copperheadhq/copperhead-quiet-orbit/images/02-bottom.png

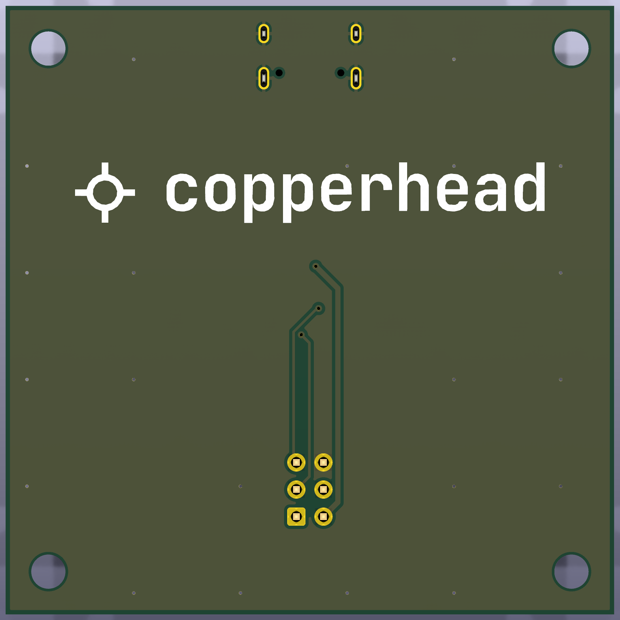
images/02-bottom.png
