copperheadhq/copperhead-quiet-orbit/images/03-iso-front-left.png

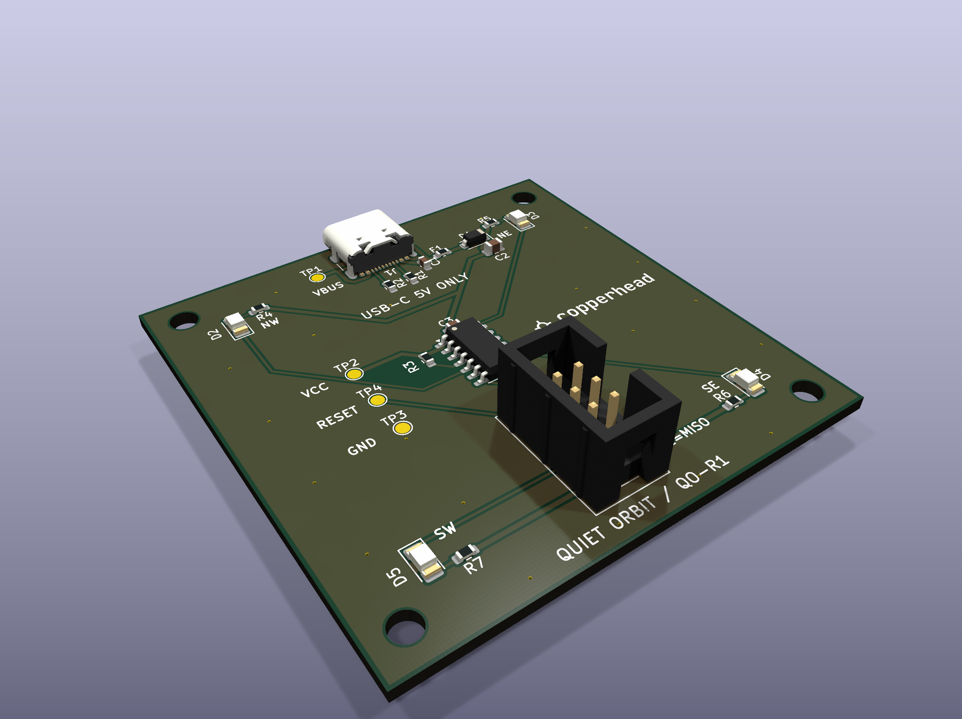
images/03-iso-front-left.png
