copperheadhq/copperhead-quiet-orbit/images/05-iso-rear-usb.png

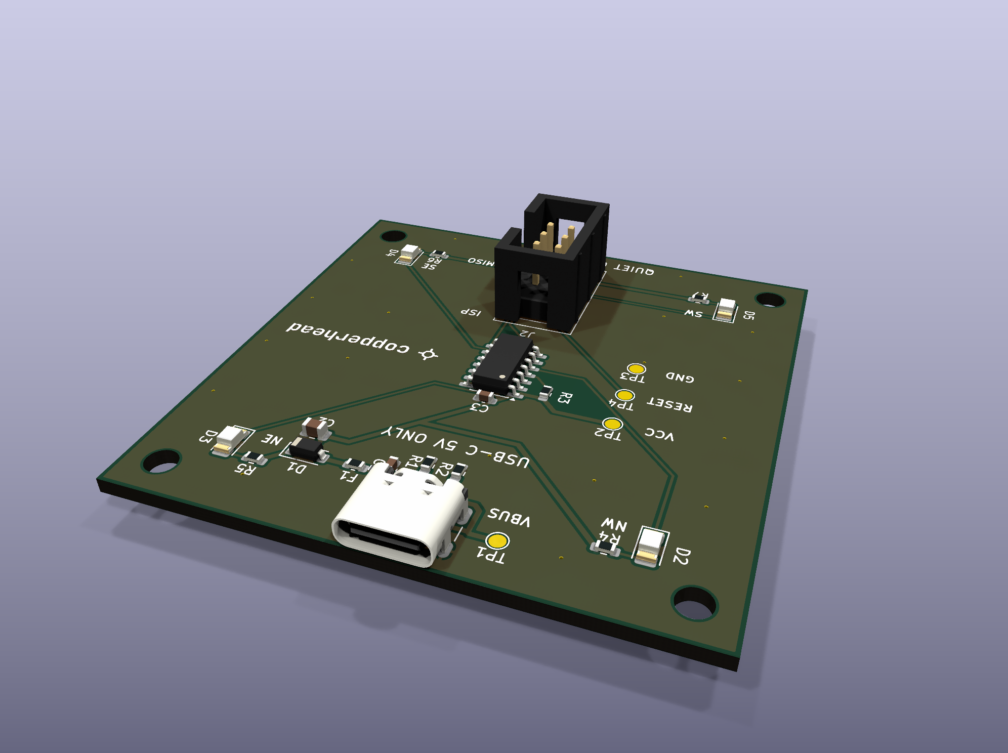
images/05-iso-rear-usb.png
