copperheadhq/copperhead-quiet-orbit/images/06-low-angle-usb.png

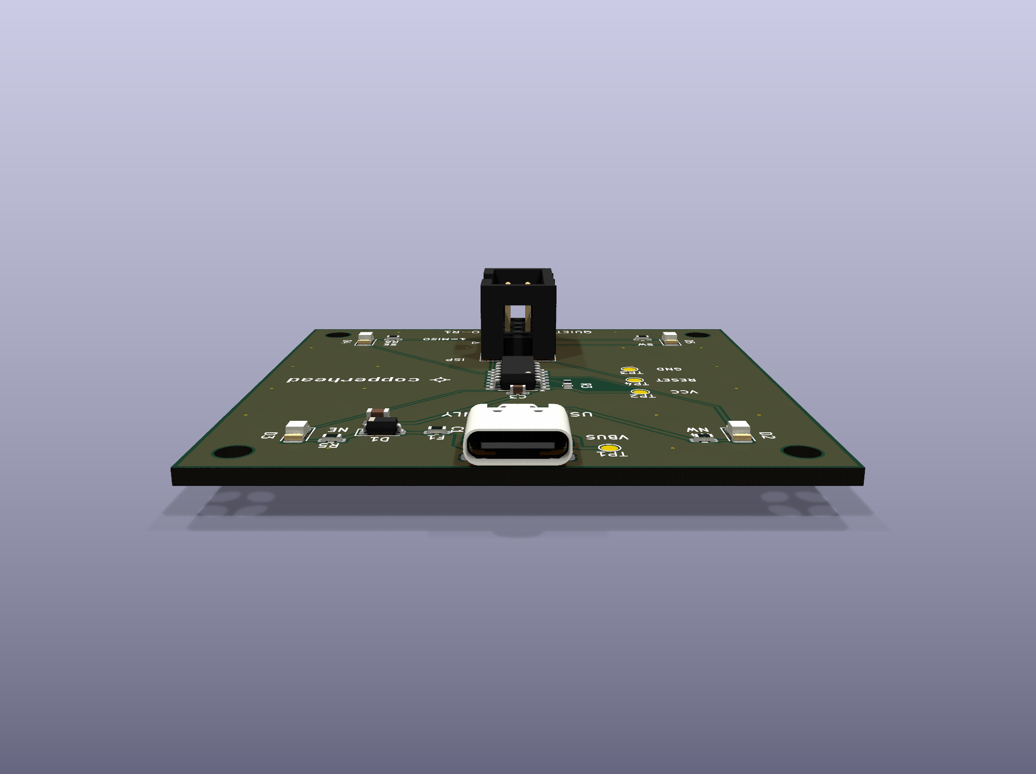
images/06-low-angle-usb.png
