copperheadhq/copperhead-quiet-orbit/images/back-angle.png

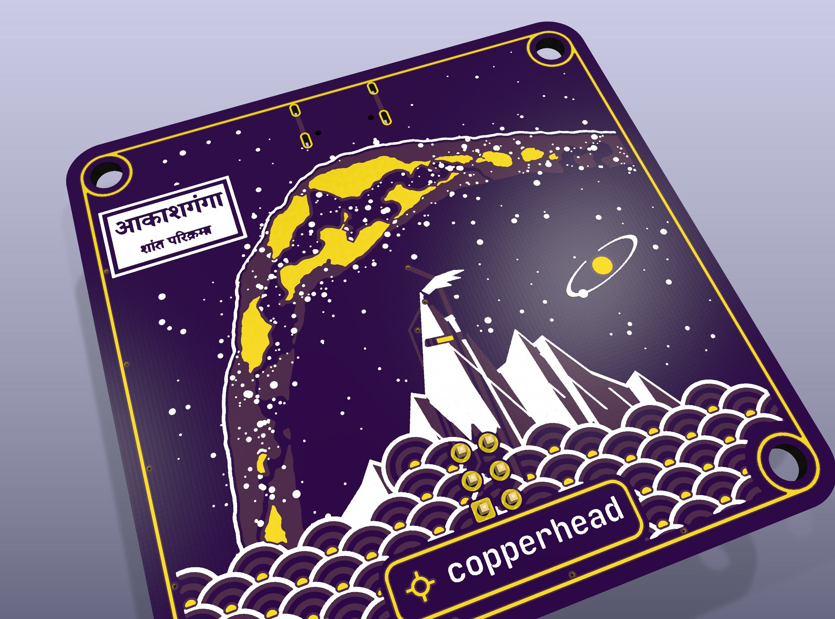
images/back-angle.png
