copperheadhq/copperhead-quiet-orbit/images/bare-milkyway-back.png

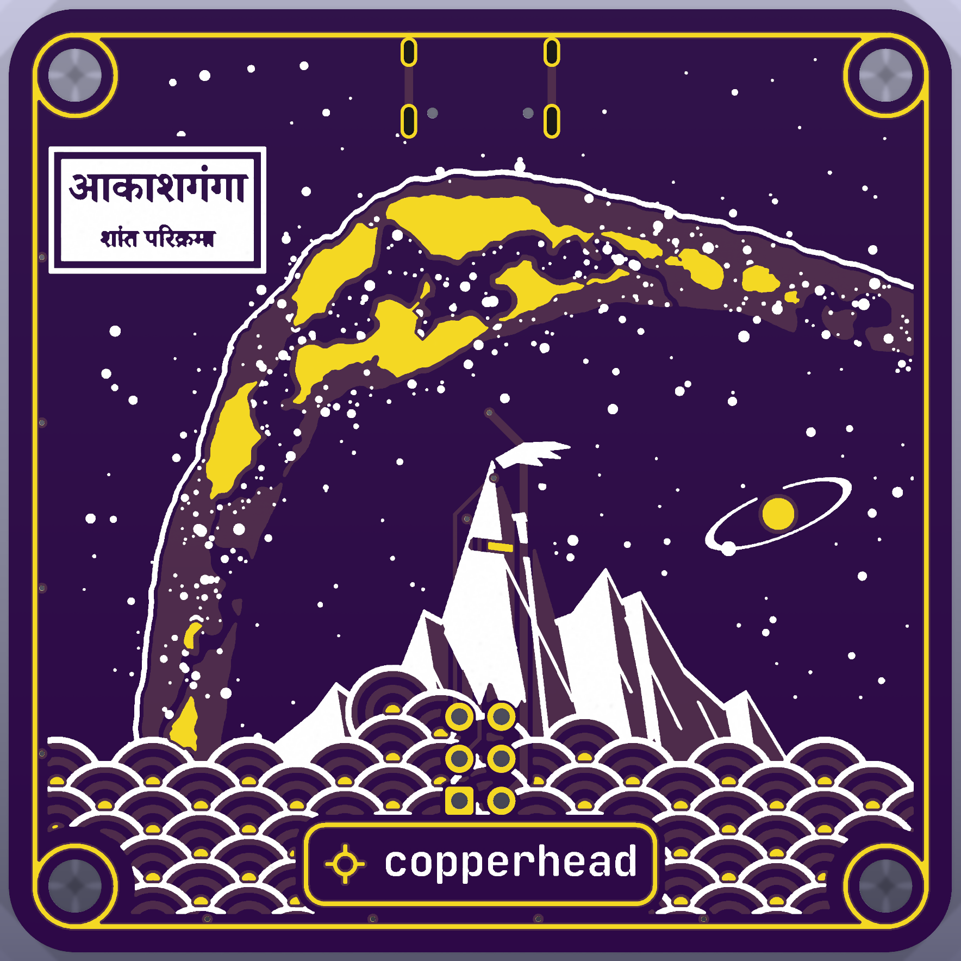
images/bare-milkyway-back.png
